t0mpr1c3/mamalala-Metcal-MX-500-remix/doc/coil_3.jpg

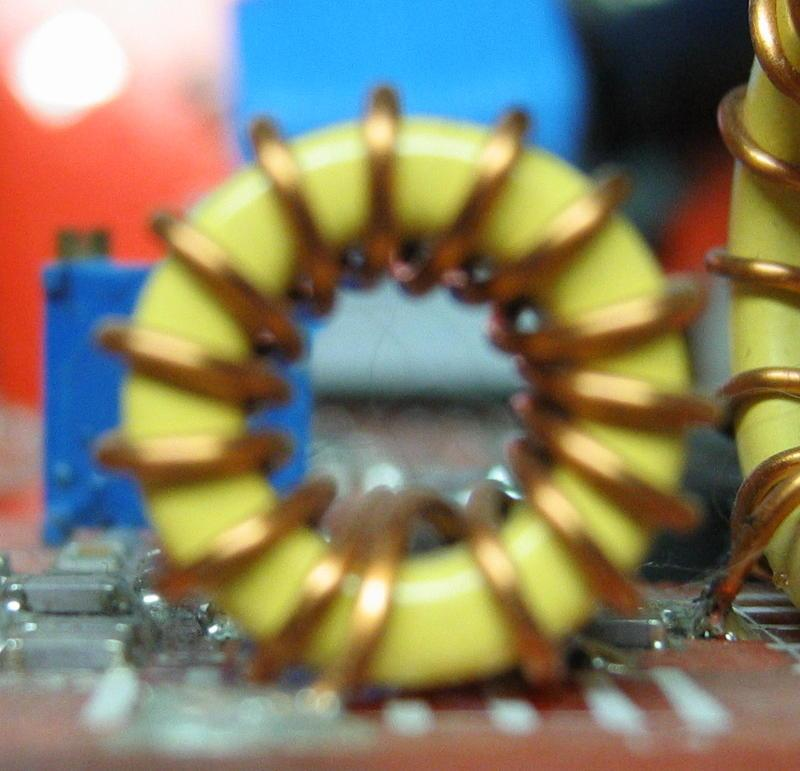
doc/coil_3.jpg
