t0mpr1c3/mamalala-Metcal-MX-500-remix/doc/randomfunprojects build/build_power.jpg

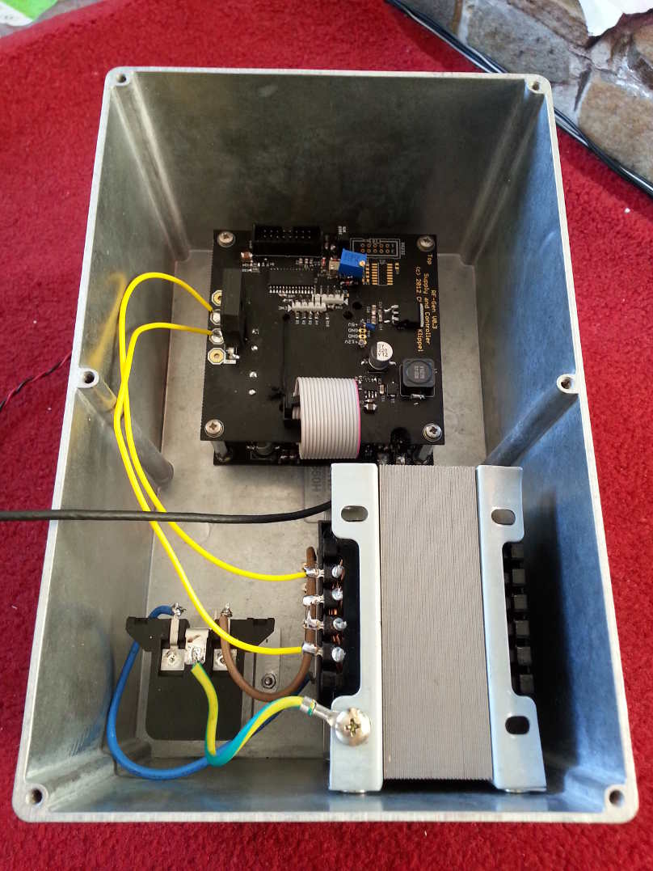
doc/randomfunprojects build/build_power.jpg
