t0mpr1c3/mamalala-Metcal-MX-500-remix/doc/randomfunprojects build/build_undervoltage_lockout_schematic.png

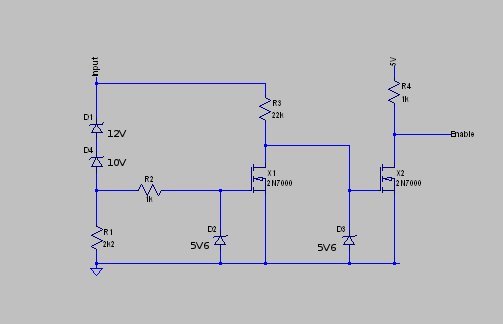
doc/randomfunprojects build/build_undervoltage_lockout_schematic.png
