t0mpr1c3/mamalala-Metcal-MX-500-remix/firmware/src/hardware/configbits.c

/*
 * (c) 2013 Ch. klippel  -  ck@atelier-klippel.de / c.klippel@gmx.de
 *
 * This code is released under the terms of the GPL, version 2 or newer.
 * See the file COPYING for more information about the license.
 *
 * Changelog:
 *
 * v00.01: - Initial version
 *
 */

#ifndef CONFIGBITS_H
#define CONFIGBITS_H

#pragma	config OSC	= INTIO67
#pragma	config FCMEN	= ON
#pragma	config IESO	= OFF
#pragma	config BOREN	= OFF
#pragma	config PWRT	= ON
#pragma	config WDT	= OFF
#pragma	config WDTPS	= 32
#pragma	config MCLRE	= ON
#pragma	config PBADEN	= ON
#pragma	config CCP2MX	= PORTBE
#pragma	config STVREN	= OFF
#pragma	config LVP	= OFF
#pragma	config XINST	= OFF
#pragma	config DEBUG	= OFF
#pragma	config CP0	= OFF
#pragma	config CP1	= OFF
#pragma	config CP2	= OFF
#pragma	config CP3	= OFF
#pragma	config CPB	= OFF
#pragma	config CPD	= OFF
#pragma	config WRT0	= OFF
#pragma	config WRT1	= OFF
#pragma	config WRT2	= OFF
#pragma	config WRT3	= OFF
#pragma	config WRTB	= OFF
#pragma	config WRTC	= OFF
#pragma	config WRTD	= OFF
#pragma	config EBTR0	= OFF
#pragma	config EBTR1	= OFF
#pragma	config EBTR2	= OFF
#pragma	config EBTR3	= OFF
#pragma	config EBTRB	= OFF

#endif
